loruro/Ultrasonic-Anemometer/src/lookupTables.h

/**
  ******************************************************************************
  * @file    lookupTables.h
  * @author  Karol Leszczyński
  * @version V1.0.0
  * @date    08-August-2015
  * @brief   Lookup tables of sin and cot functions.
  ******************************************************************************
  * @attention
  *
  * This file is part of Ultrasonic_Anemometer.
  *
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
  ******************************************************************************
  */

#ifndef LOOKUPTABLES_H_
#define LOOKUPTABLES_H_

#include <avr/pgmspace.h>

const uint8_t sinSqTable[] PROGMEM = {0x0, 0x0, 0x0, 0x0, 0x0, 0x0, 0x0, 0x0, 0x0, 0x0, 0x0, 0x0, 0x0, 0x0, 0x0, 0x0, 0x0, 0x0, 0x0, 0x0, 0x0, 0x0, 0x0, 0x0, 0x0, 0x0, 0x0, 0x0, 0x0, 0x0, 0x0, 0x0, 0x0, 0x0, 0x0, 0x0, 0x0, 0x0, 0x0, 0x0, 0x0, 0x0, 0x0, 0x0, 0x0, 0x1, 0x1, 0x1, 0x1, 0x1, 0x1, 0x1, 0x1, 0x1, 0x1, 0x1, 0x1, 0x1, 0x1, 0x1, 0x1, 0x1, 0x1, 0x1, 0x1, 0x1, 0x1, 0x1, 0x1, 0x1, 0x1, 0x1, 0x1, 0x1, 0x1, 0x1, 0x1, 0x2, 0x2, 0x2, 0x2, 0x2, 0x2, 0x2, 0x2, 0x2, 0x2, 0x2, 0x2, 0x2, 0x2, 0x2, 0x2, 0x2, 0x2, 0x2, 0x2, 0x2, 0x2, 0x2, 0x3, 0x3, 0x3, 0x3, 0x3, 0x3, 0x3, 0x3, 0x3, 0x3, 0x3, 0x3, 0x3, 0x3, 0x3, 0x3, 0x3, 0x3, 0x4, 0x4, 0x4, 0x4, 0x4, 0x4, 0x4, 0x4, 0x4, 0x4, 0x4, 0x4, 0x4, 0x4, 0x4, 0x4, 0x5, 0x5, 0x5, 0x5, 0x5, 0x5, 0x5, 0x5, 0x5, 0x5, 0x5, 0x5, 0x5, 0x5, 0x6, 0x6, 0x6, 0x6, 0x6, 0x6, 0x6, 0x6, 0x6, 0x6, 0x6, 0x6, 0x6, 0x7, 0x7, 0x7, 0x7, 0x7, 0x7, 0x7, 0x7, 0x7, 0x7, 0x7, 0x7, 0x8, 0x8, 0x8, 0x8, 0x8, 0x8, 0x8, 0x8, 0x8, 0x8, 0x8, 0x9, 0x9, 0x9, 0x9, 0x9, 0x9, 0x9, 0x9, 0x9, 0x9, 0x9, 0xa, 0xa, 0xa, 0xa, 0xa, 0xa, 0xa, 0xa, 0xa, 0xa, 0xb, 0xb, 0xb, 0xb, 0xb, 0xb, 0xb, 0xb, 0xb, 0xc, 0xc, 0xc, 0xc, 0xc, 0xc, 0xc, 0xc, 0xc, 0xc, 0xd, 0xd, 0xd, 0xd, 0xd, 0xd, 0xd, 0xd, 0xd, 0xe, 0xe, 0xe, 0xe, 0xe, 0xe, 0xe, 0xe, 0xf, 0xf, 0xf, 0xf, 0xf, 0xf, 0xf, 0xf, 0xf, 0x10, 0x10, 0x10, 0x10, 0x10, 0x10, 0x10, 0x10, 0x11, 0x11, 0x11, 0x11, 0x11, 0x11, 0x11, 0x11, 0x12, 0x12, 0x12, 0x12, 0x12, 0x12, 0x12, 0x13, 0x13, 0x13, 0x13, 0x13, 0x13, 0x13, 0x13, 0x14, 0x14, 0x14, 0x14, 0x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
 0x2, 0x1, 0x1, 0x1, 0x1, 0x1, 0x1, 0x1, 0x1, 0x1, 0x1, 0x1, 0x1, 0x1, 0x1, 0x1, 0x1, 0x1, 0x1, 0x1, 0x1, 0x1, 0x1, 0x1, 0x1, 0x1, 0x1, 0x1, 0x1, 0x1, 0x1, 0x1, 0x1, 0x1, 0x0, 0x0, 0x0, 0x0, 0x0, 0x0, 0x0, 0x0, 0x0, 0x0, 0x0, 0x0, 0x0, 0x0, 0x0, 0x0, 0x0, 0x0, 0x0, 0x0, 0x0, 0x0, 0x0, 0x0, 0x0, 0x0, 0x0, 0x0, 0x0, 0x0, 0x0, 0x0, 0x0, 0x0, 0x0, 0x0, 0x0, 0x0, 0x0, 0x0, 0x0, 0x0, 0x0, 0x0};
const uint32_t cotTable_1[] PROGMEM = {0x7fffffff, 0x2faf080, 0x17d7840, 0xfe502b, 0xbebc20, 0x989680, 0x7f2815, 0x6cfdc9, 0x5f5e10, 0x54c564, 0x4c4b40, 0x455baf, 0x3f940b, 0x3ab00a, 0x367ee5, 0x32dcd5, 0x2faf08, 0x2ce0f8, 0x2a62b2, 0x28279b, 0x2625a0, 0x245498, 0x22add7, 0x212bd9, 0x1fca05, 0x1e8480, 0x1d5805, 0x1c41cc, 0x1b3f72, 0x1a4eea, 0x196e6b, 0x189c67, 0x17d784, 0x171e8f, 0x16707c, 0x15cc5b, 0x153159, 0x149eb7, 0x1413cd, 0x139003, 0x1312d0, 0x129bb8, 0x122a4c, 0x11be27, 0x1156ec, 0x10f447, 0x1095ec, 0x103b96, 0xfe503, 0xf91f8, 0xf4240, 0xef5a8, 0xeac02, 0xe6524, 0xe20e6, 0xddf23, 0xd9fb9, 0xd6289, 0xd2775, 0xcee62, 0xcb735, 0xc81d8, 0xc4e34, 0xc1c33, 0xbebc2, 0xbbccf, 0xb8f48, 0xb631d, 0xb383e, 0xb0e9e, 0xae62e, 0xabee1, 0xa98ac, 0xa7383, 0xa4f5c, 0xa2c2b, 0xa09e7, 0x9e887, 0x9c802, 0x9a84f, 0x98968, 0x96b44, 0x94ddc, 0x9312a, 0x91526, 0x8f9cb, 0x8df13, 0x8c4f8, 0x8ab76, 0x89286, 0x87a23, 0x8624a, 0x84af6, 0x83422, 0x81dcb, 0x807ec, 0x7f281, 0x7dd88, 0x7c8fc, 0x7b4da, 0x7a120, 0x78dc9, 0x77ad4, 0x7683d, 0x75601, 0x7441e, 0x73292, 0x7215a, 0x71073, 0x6ffdb, 0x6ef91, 0x6df92, 0x6cfdc, 0x6c06e, 0x6b144, 0x6a25e, 0x693ba, 0x68556, 0x67731, 0x66948, 0x65b9a, 0x64e27, 0x640ec, 0x633e8, 0x6271a, 0x61a80, 0x60e19, 0x601e5, 0x5f5e1, 0x5ea0d, 0x5de67, 0x5d2ef, 0x5c7a4, 0x5bc84, 0x5b18e, 0x5a6c2, 0x59c1f, 0x591a3, 0x5874f, 0x57d20, 0x57317, 0x56932, 0x55f70, 0x555d2, 0x54c56, 0x542fb, 0x539c2, 0x530a8, 0x527ae, 0x51ed2, 0x51615, 0x50d76, 0x504f3, 0x4fc8d, 0x4f443, 0x4ec14, 0x4e4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
bfda, 0xbfaa, 0xbf7a, 0xbf4a, 0xbf1a, 0xbeea, 0xbeba, 0xbe8b, 0xbe5b, 0xbe2c, 0xbdfc, 0xbdcd, 0xbd9e, 0xbd6f, 0xbd40, 0xbd11, 0xbce2, 0xbcb3, 0xbc85, 0xbc56, 0xbc28, 0xbbf9, 0xbbcb, 0xbb9d, 0xbb6f, 0xbb41, 0xbb13, 0xbae5, 0xbab7};
const uint16_t cotTable_2[] PROGMEM = {0xba81, 0xb8bd, 0xb702, 0xb54f, 0xb3a4, 0xb201, 0xb065, 0xaed1, 0xad44, 0xabbe, 0xaa3f, 0xa8c6, 0xa754, 0xa5e8, 0xa482, 0xa322, 0xa1c8, 0xa074, 0x9f25, 0x9ddc, 0x9c98, 0x9b59, 0x9a1f, 0x98ea, 0x97ba, 0x968e, 0x9568, 0x9445, 0x9327, 0x920d, 0x90f8, 0x8fe6, 0x8ed9, 0x8dcf, 0x8cca, 0x8bc8, 0x8ac9, 0x89cf, 0x88d7, 0x87e4, 0x86f3, 0x8606, 0x851c, 0x8435, 0x8352, 0x8271, 0x8194, 0x80b9, 0x7fe1, 0x7f0c, 0x7e3a, 0x7d6a, 0x7c9d, 0x7bd3, 0x7b0b, 0x7a46, 0x7983, 0x78c3, 0x7805, 0x7749, 0x7690, 0x75d9, 0x7524, 0x7471, 0x73c0, 0x7312, 0x7265, 0x71ba, 0x7112, 0x706b, 0x6fc6, 0x6f23, 0x6e82, 0x6de3, 0x6d46, 0x6caa, 0x6c10, 0x6b78, 0x6ae1, 0x6a4c, 0x69b9, 0x6927, 0x6897, 0x6808, 0x677b, 0x66ef, 0x6665, 0x65dd, 0x6555, 0x64cf, 0x644b, 0x63c7, 0x6346, 0x62c5, 0x6246, 0x61c8, 0x614b, 0x60d0, 0x6055, 0x5fdc, 0x5f64, 0x5eed, 0x5e78, 0x5e03, 0x5d90, 0x5d1e, 0x5cad, 0x5c3d, 0x5bce, 0x5b60, 0x5af3, 0x5a87, 0x5a1c, 0x59b2, 0x5949, 0x58e1, 0x5879, 0x5813, 0x57ae, 0x574a, 0x56e6, 0x5684, 0x5622, 0x55c1, 0x5561, 0x5502, 0x54a3, 0x5446, 0x53e9, 0x538d, 0x5332, 0x52d8, 0x527e, 0x5225, 0x51cd, 0x5176, 0x511f, 0x50c9, 0x5074, 0x501f, 0x4fcb, 0x4f78, 0x4f26, 0x4ed4, 0x4e83, 0x4e32, 0x4de2, 0x4d93, 0x4d45, 0x4cf7, 0x4ca9, 0x4c5c, 0x4c10, 0x4bc5, 0x4b7a, 0x4b2f, 0x4ae5, 0x4a9c, 0x4a53, 0x4a0b, 0x49c3, 0x497c, 0x4936, 0x48f0, 0x48aa, 0x4865, 0x4821, 0x47dd, 0x4799, 0x4756, 0x4714, 0x46d2, 0x4690, 0x464f, 0x460f, 0x45ce, 0x458f, 0x454f, 0x4511, 0x44d2, 0x4494, 0x4457, 0x441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
